maxschommer/BalancingBusinessCard/Design/BalancingBusinessCard/BalancingBusinessCard.sch

## KiCad design Design/BalancingBusinessCard/BalancingBusinessCard.sch (2018-11-12)

Schematic: BalancingBusinessCard.sch

Parts:
BT101: Battery
C101, C102: 10uF; C_0805_2012Metric
ICSP1: Conn_02x03_Odd_Even; PinHeader_2x03_P2.54mm_Vertical
J101: TestPoints; Testpoint_1x10
U101: ATtiny261-20SU; SOIC-20W_7.5x12.8mm_P1.27mm

Notes on the sheet:
+3V
